crankery/crank68/src/emu/rom.cpp

#include "rom.h"
#include "machine.h"

uint8_t Rom::read(uint16_t addr) const
{
    if (addr >= startAddress_ && addr <= endAddress_)
    {
        return memory_[addr - startAddress_];
    }

    return 0xff;
}

void Rom::write(uint16_t addr, uint8_t value)
{
    if (addr >= startAddress_ && addr <= endAddress_)
    {
        memory_[addr - startAddress_] = value;
    }
}
